SolderedElectronics/1-channel-relay-board-with-easyC-hardware-design/OUTPUTS/V1.1.1/333021.jpg

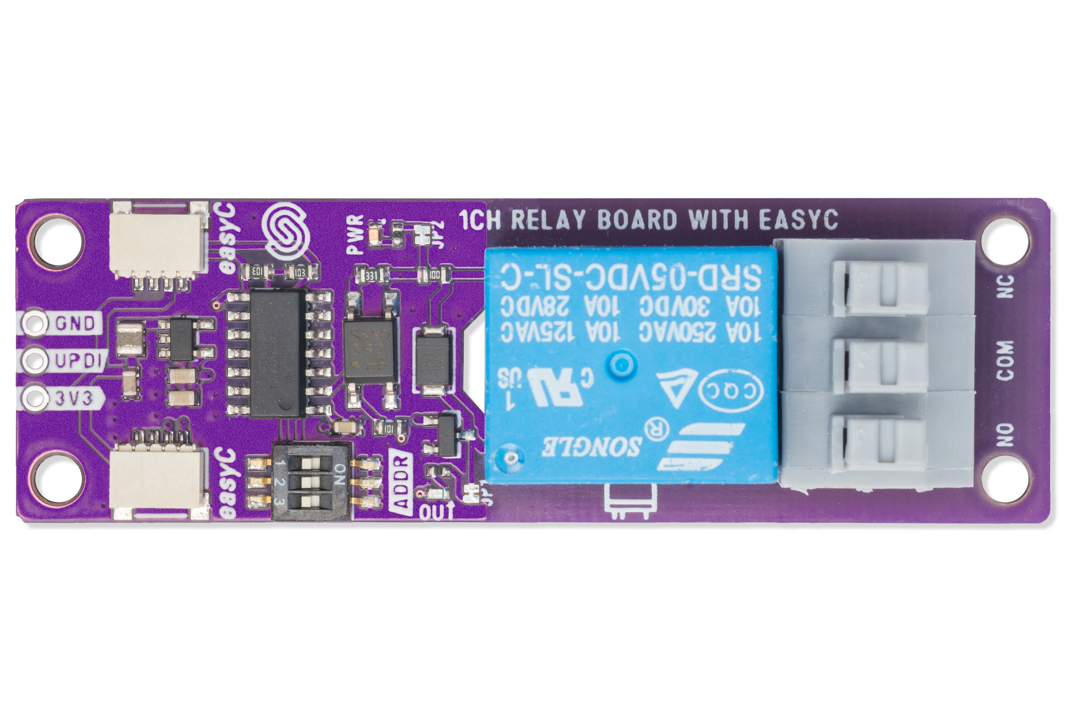
OUTPUTS/V1.1.1/333021.jpg
