SolderedElectronics/1-channel-relay-board-with-easyC-hardware-design/OUTPUTS/V1.1.1/1CH relay board with easyC Pinout.jpg

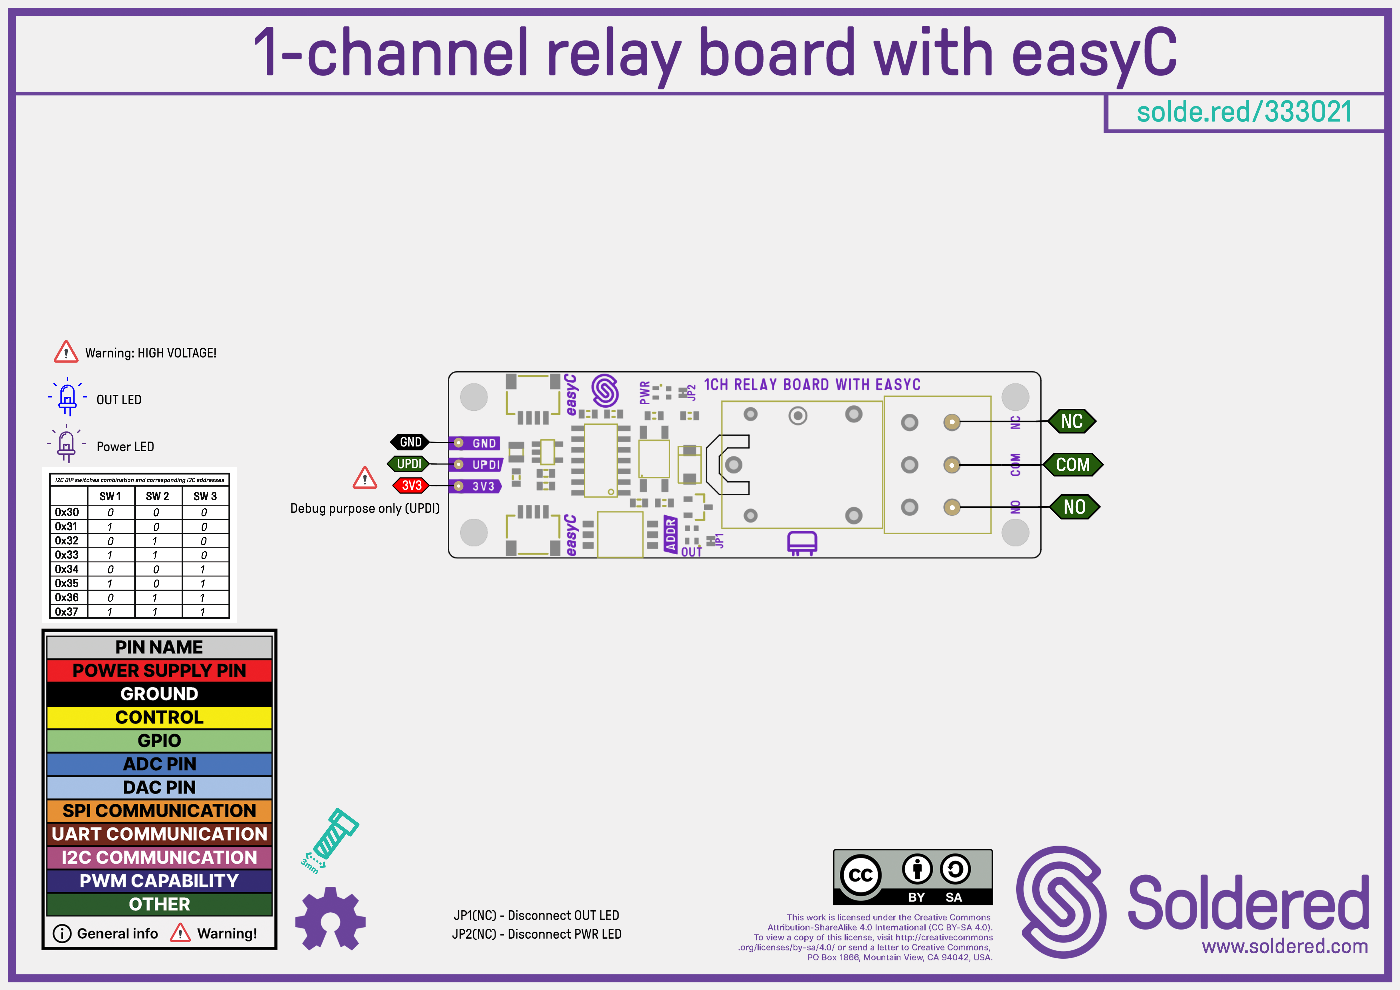
OUTPUTS/V1.1.1/1CH relay board with easyC Pinout.jpg
